dennuguyen/sumoltaneous-equations/README/timeline.jpg

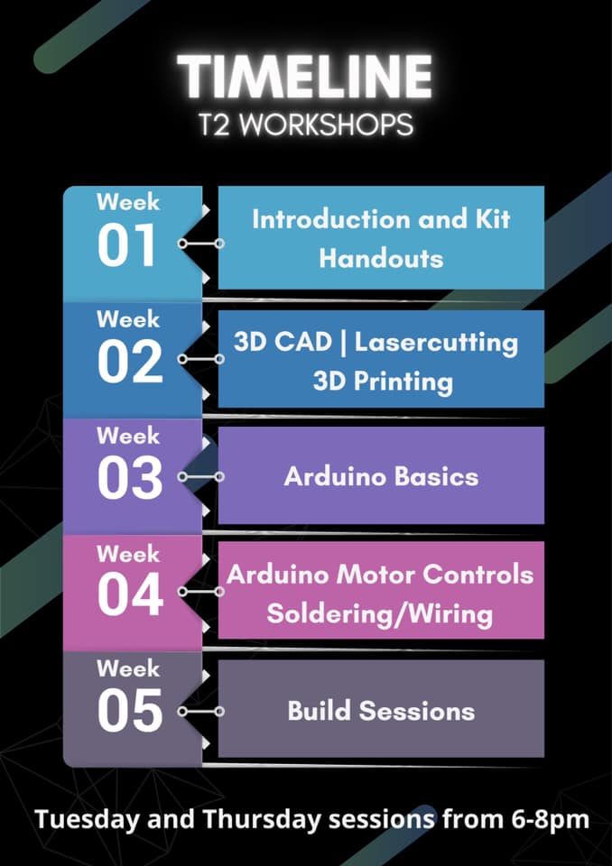
README/timeline.jpg
