dennuguyen/sumoltaneous-equations/README/tournament-rules.jpg

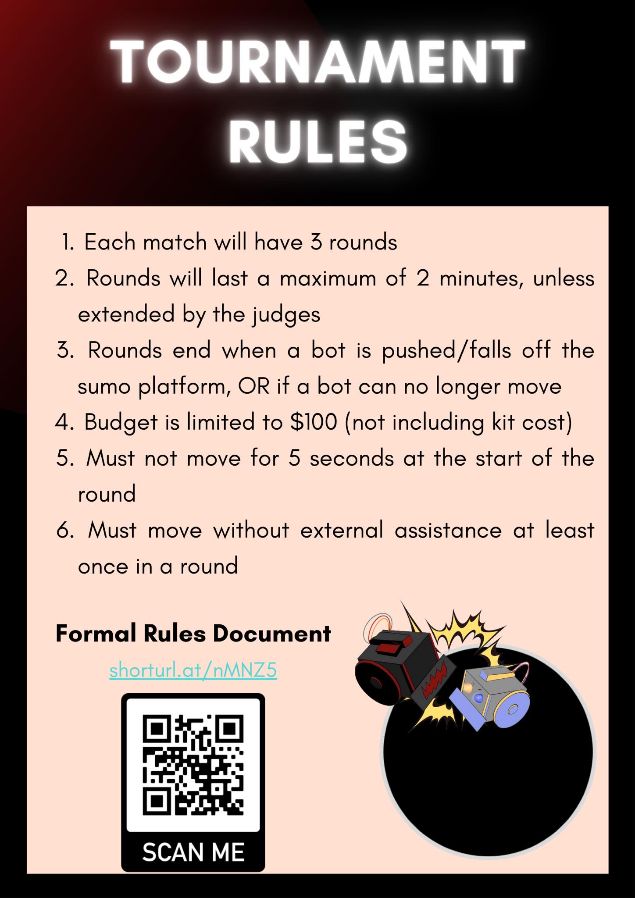
README/tournament-rules.jpg
