dennuguyen/sumoltaneous-equations/sumoltaneous-equations-inventor-sheet-metal/All.png

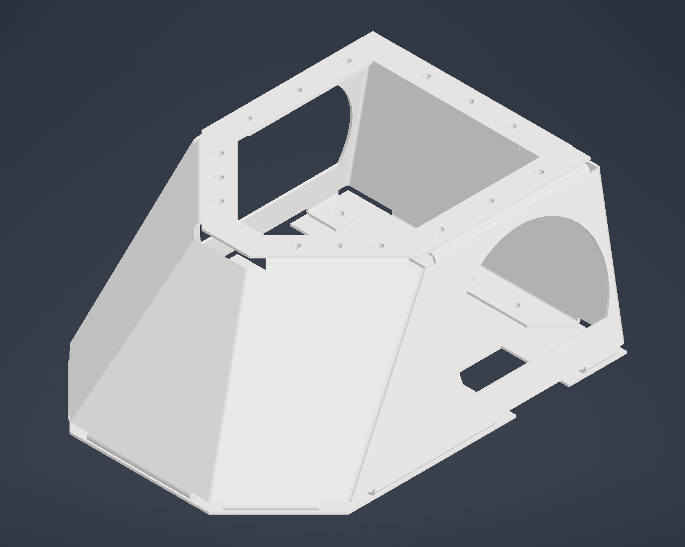
sumoltaneous-equations-inventor-sheet-metal/All.png
