dennuguyen/sumoltaneous-equations/sumoltaneous-equations-inventor-sheet-metal/Top.png

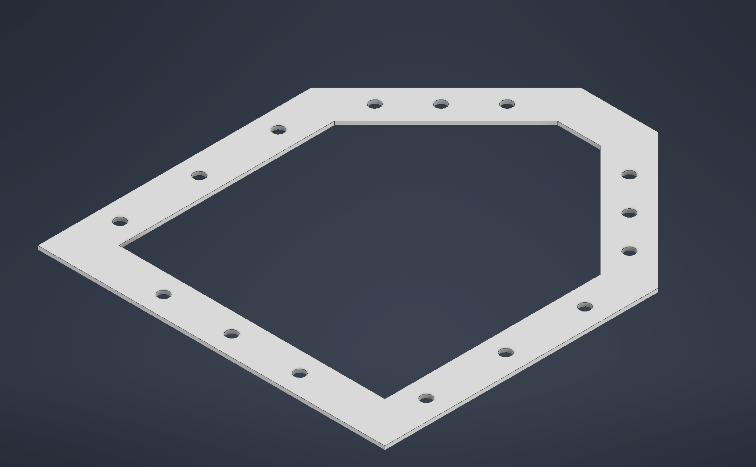
sumoltaneous-equations-inventor-sheet-metal/Top.png
