dennuguyen/sumoltaneous-equations/sumoltaneous-equations-inventor-sheet-metal/Assembly.png

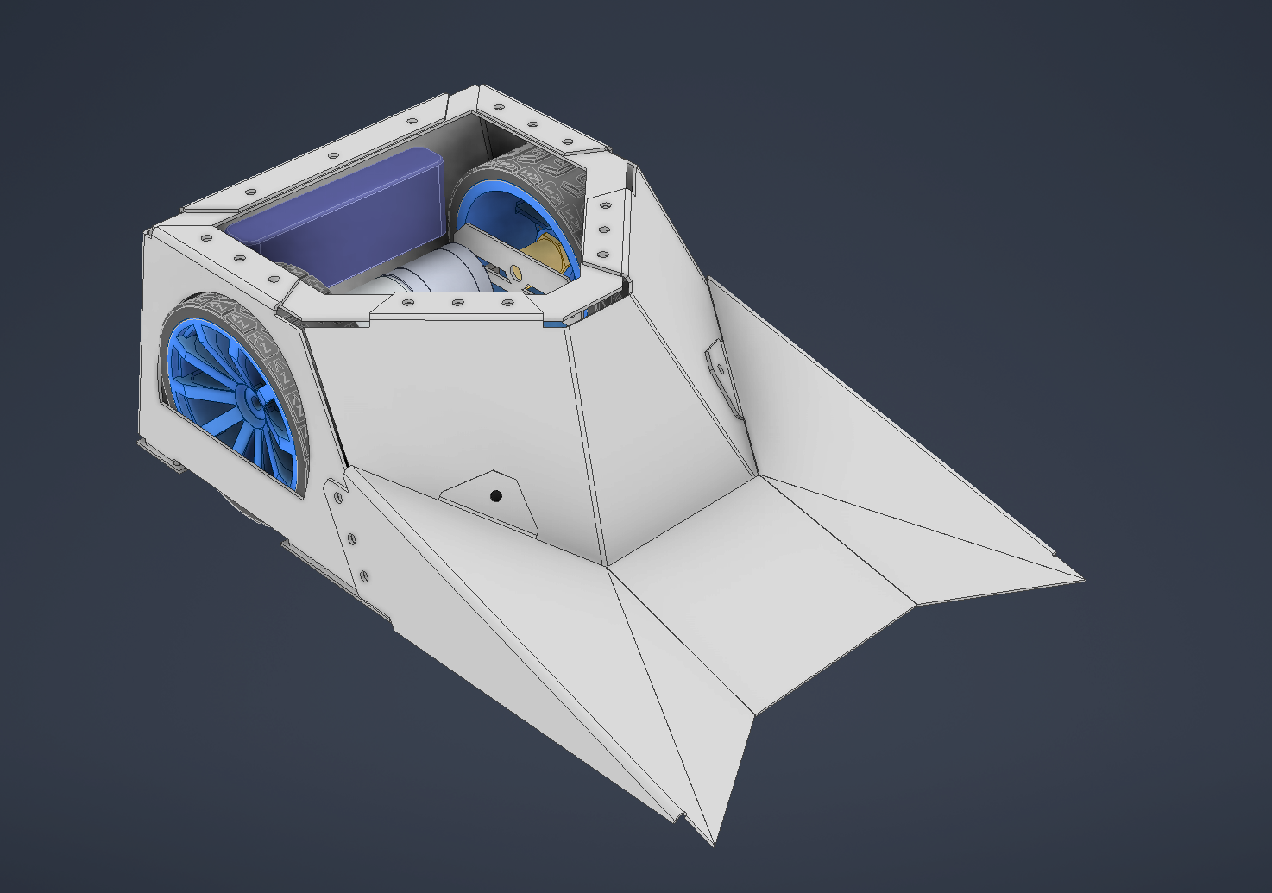
sumoltaneous-equations-inventor-sheet-metal/Assembly.png
